ionos-sdr/ionos-sdr-mini/CAD/ionosmini_1v0/ionosSDR_mini.kicad_sch

## KiCad design CAD/ionosmini_1v0/ionosSDR_mini.kicad_sch (2026-10-02, an earlier design)

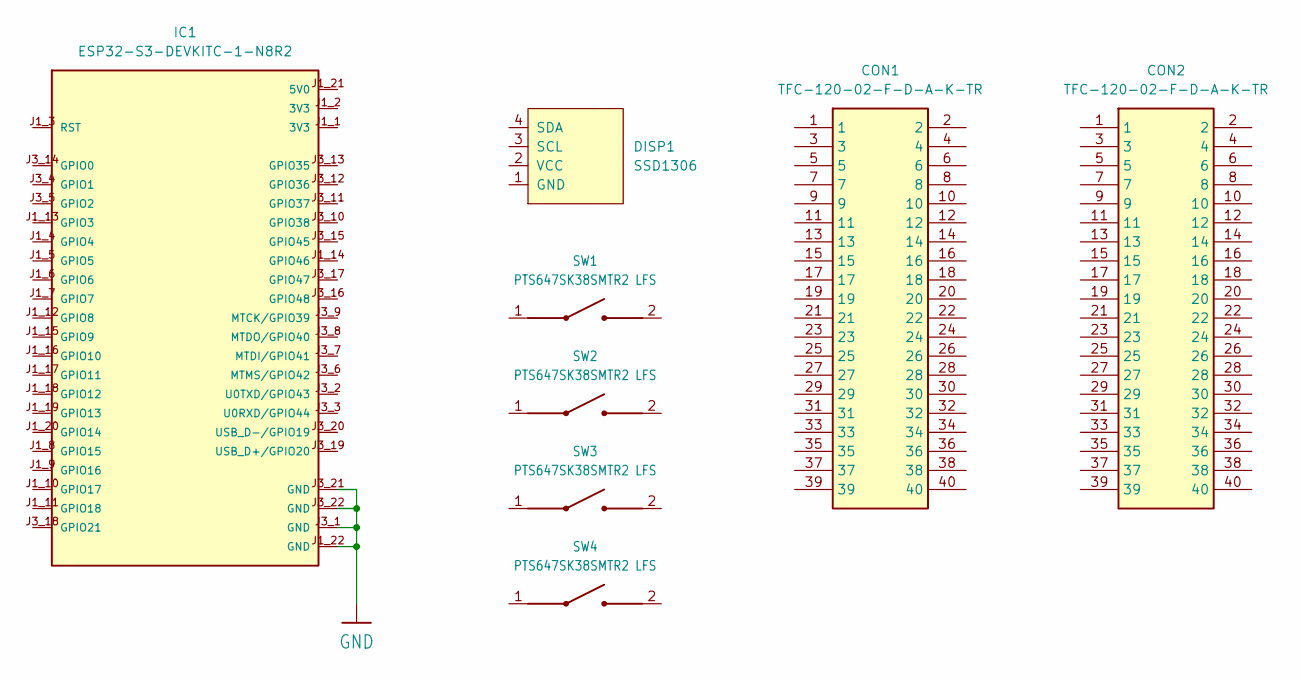
[picture p8: schematic ionosSDR_mini.kicad_sch]

Parts:
CON1, CON2: TFC-120-02-F-D-A-K-TR; TFC-120-02-XX-D-A-K-TR; MPN TFC-120-02-F-D-A-K-TR
DISP1: SSD1306; 128x64OLED; MPN OLED 4pin BLUE
IC1: ESP32-S3-DEVKITC-1-N8R2; XCVR_ESP32-S3-DEVKITC-1-N8R2; MPN ESP32-S3-DEVKITC-1-N8R2
SW1, SW2, SW3, SW4: PTS647SK38SMTR2 LFS; PTS647SK38SMTR2LFS; MPN PTS647SK38SMTR2 LFS

Connections:
GND: IC1.J1_22 (GND), IC1.J3_1 (GND), IC1.J3_21 (GND), IC1.J3_22 (GND)
